SimonBauer-git/lxardoscope_wemos_d1_mini/schematic/image_1.jpg

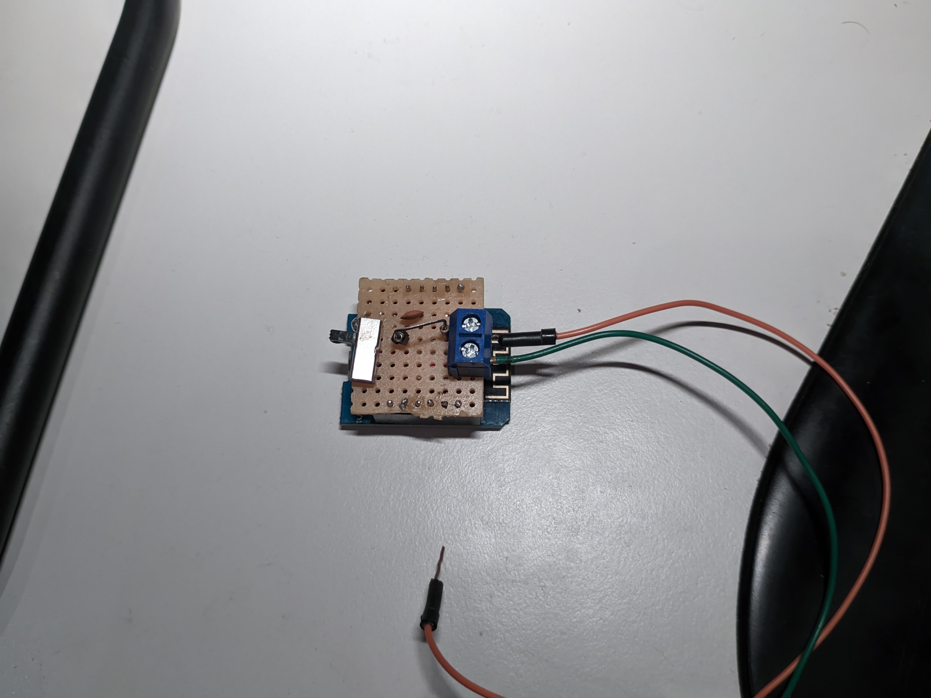
schematic/image_1.jpg
