SimonBauer-git/lxardoscope_wemos_d1_mini/schematic/wemos shield v2/wemos_shield.kicad_sch

## KiCad design schematic/wemos shield v2/wemos_shield.kicad_sch (2024-02-22)

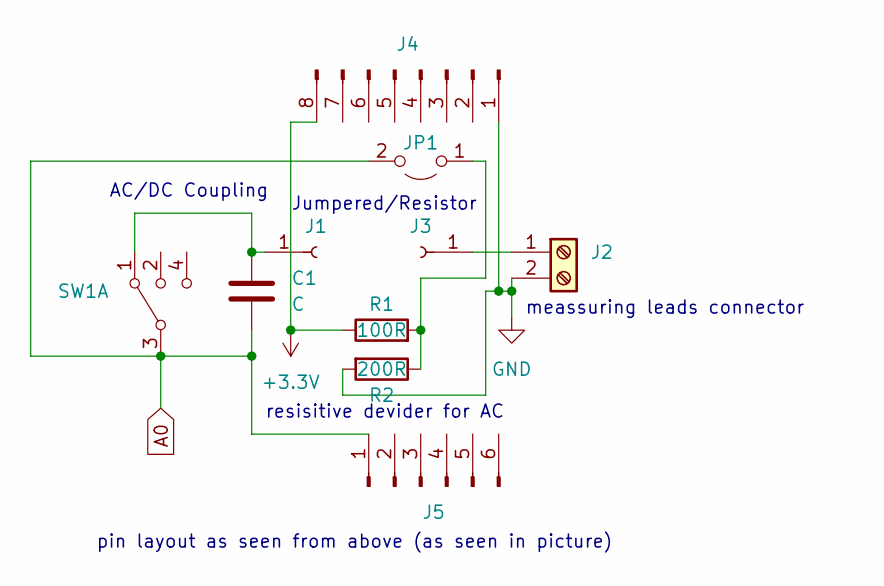
[picture p5: schematic wemos_shield.kicad_sch]

Parts:
C1: C
J1, J3: Conn_01x01_Socket
J2: Screw_Terminal_01x02
J4: (no value)
J5: Conn_01x06_Pin
JP1: (no value)
R1: 100R
R2: 200R
SW1: SW_DP3T

Connections:
+3.3V: J4.8, R1.1
A0: C1.2, J5.1, JP1.2 (B), SW1.3
GND: J2.2, J4.1, R2.2
unnamed: C1.1, J1.1, SW1.1
unnamed: J2.1, J3.1
unnamed: JP1.1 (A), R1.2, R2.1

Notes on the sheet:
meassuring leads connector
resisitive devider for AC
Jumpered/Resistor
pin layout as seen from above (as seen in picture)
AC/DC Coupling
